nguyenvince/myAQM/Portable air quality monitor/images/pcb/myaqm-pcb-2d-render.png

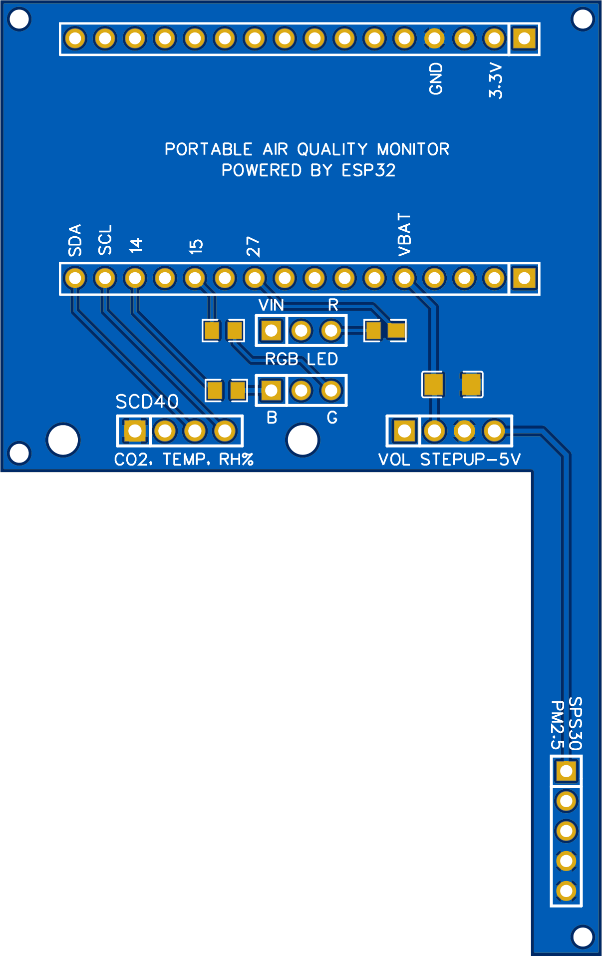
Portable air quality monitor/images/pcb/myaqm-pcb-2d-render.png
