nguyenvince/myAQM/Portable air quality monitor/images/pcb/myaqm-pcb-3d-render.png

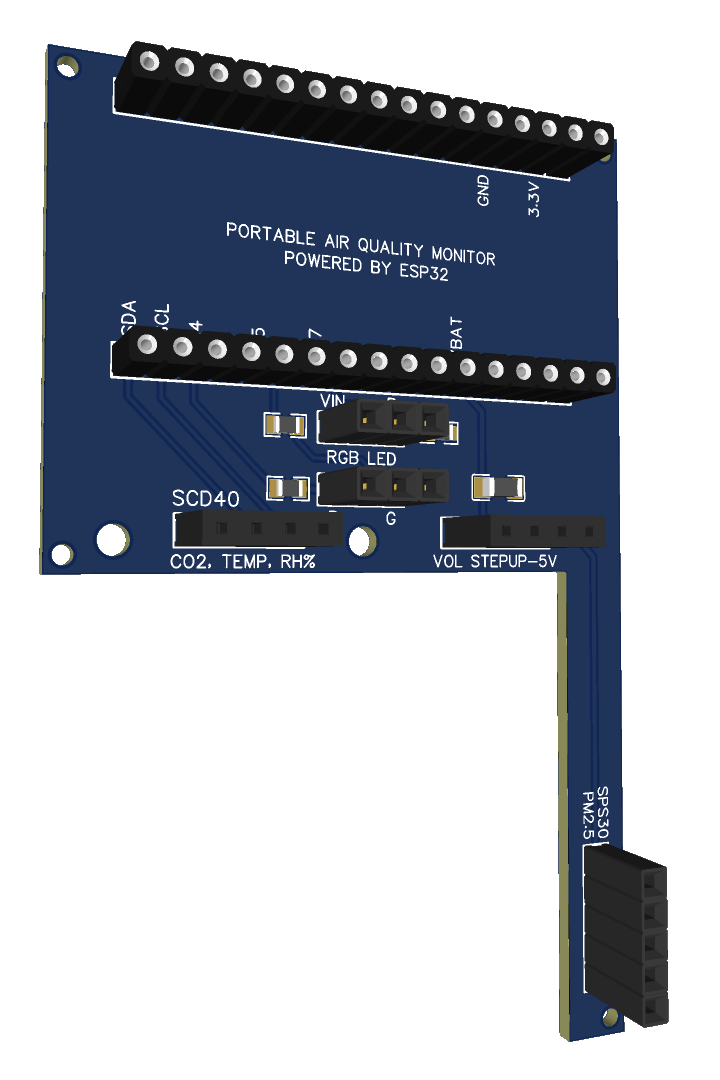
Portable air quality monitor/images/pcb/myaqm-pcb-3d-render.png
