nguyenvince/myAQM/Portable air quality monitor/images/renders/overview.png

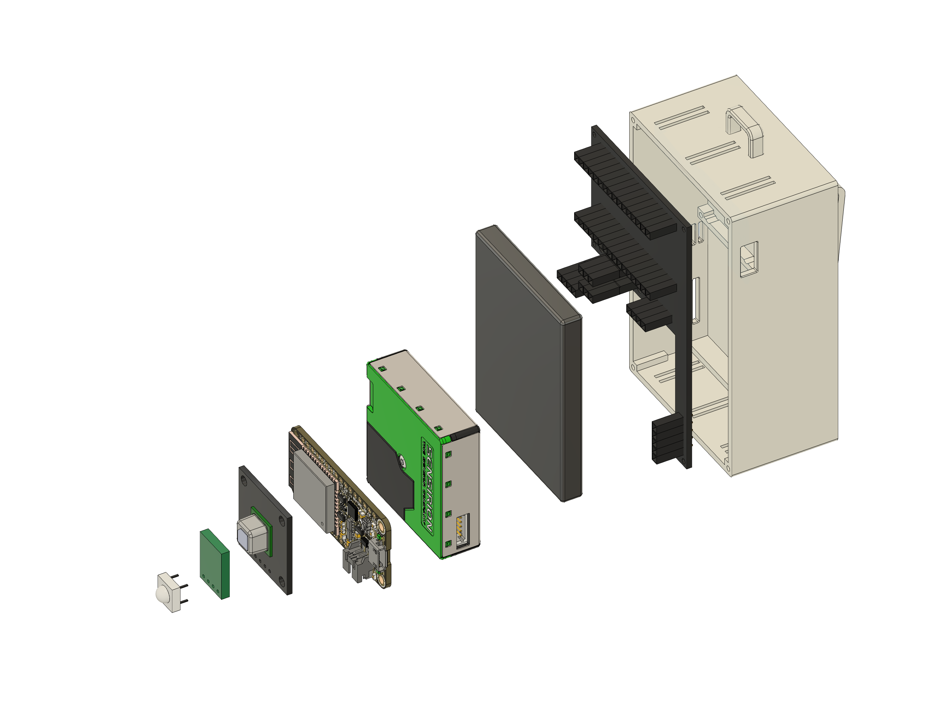
Portable air quality monitor/images/renders/overview.png
