nguyenvince/myAQM/Portable air quality monitor/images/electronics/pololu-5v-step-up-voltage-regulator-u1v11f5.jpg

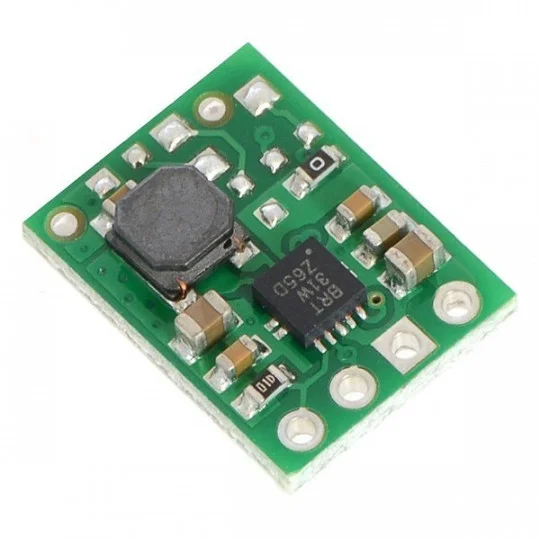
Portable air quality monitor/images/electronics/pololu-5v-step-up-voltage-regulator-u1v11f5.jpg
